dlip/harite-v3/freecad/caps-stickstem09.step

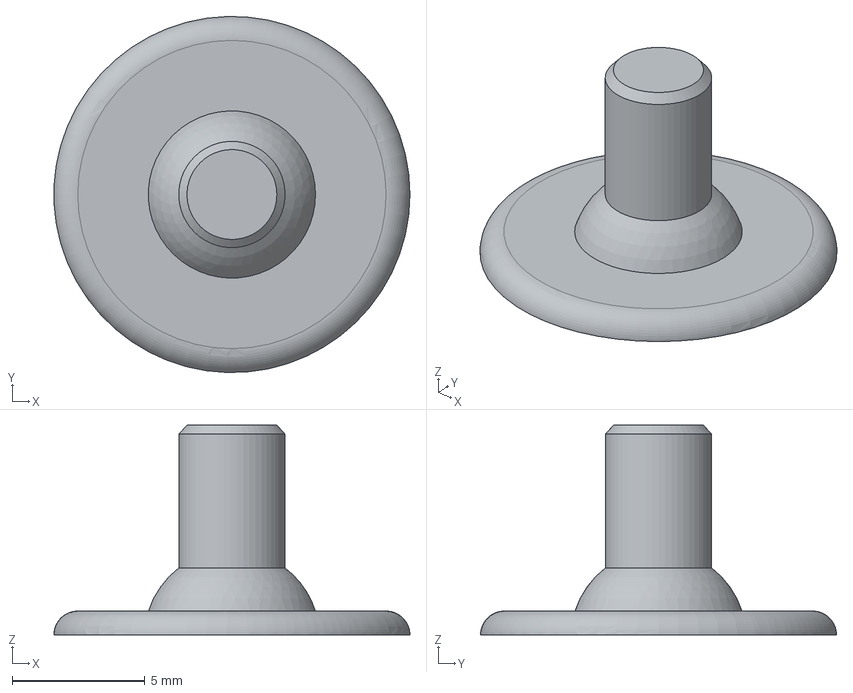
[picture p17: CAD file, 2025-07-30]
freecad/caps-stickstem09.step
13.4 x 13.4 x 7.90 mm
