dlip/harite-v3/freecad/caps-stickstem11.step

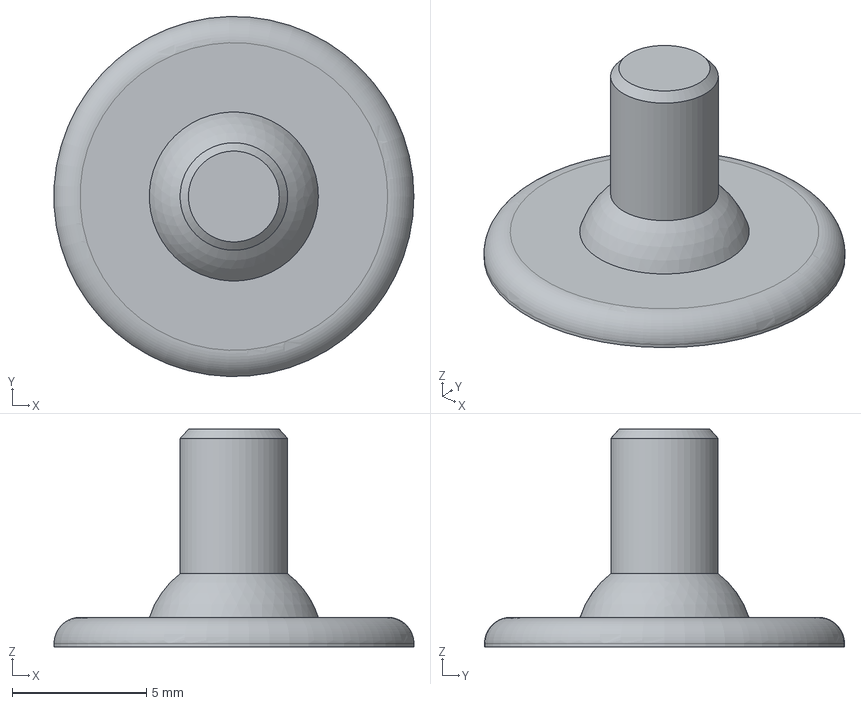
[picture p18: CAD file, 2025-07-30]
freecad/caps-stickstem11.step
13.4 x 13.4 x 8.10 mm
