dlip/harite-v3/freecad/caps-stickstem10.step

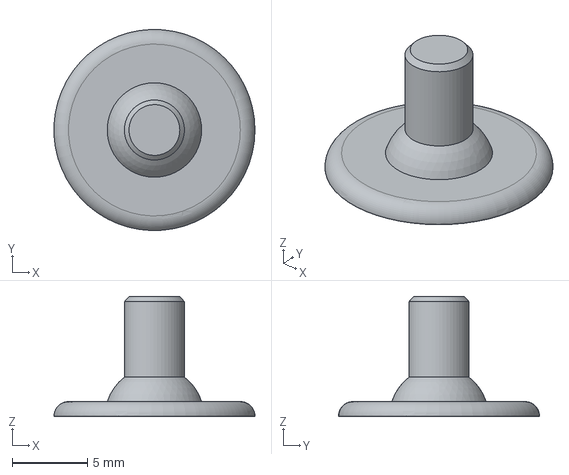
[picture p19: CAD file, 2025-07-30]
freecad/caps-stickstem10.step
13.4 x 13.4 x 8.00 mm
