dlip/harite-v3/freecad/thumb-cluster-casebase-print.step

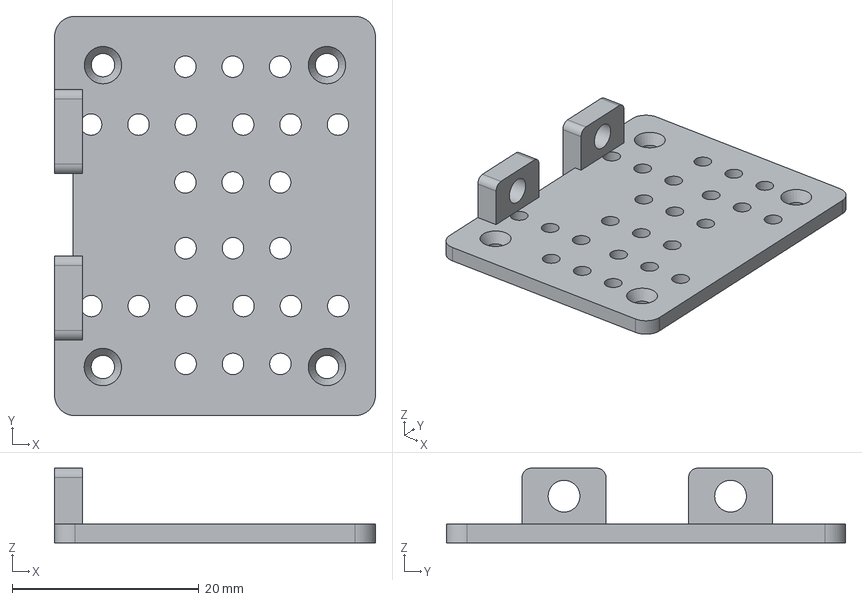
[picture p20: CAD file, 2025-07-30]
freecad/thumb-cluster-casebase-print.step
34.4 x 42.8 x 8.00 mm
