dlip/harite-v3/freecad/thumb-cluster-casetop-stick-print.step

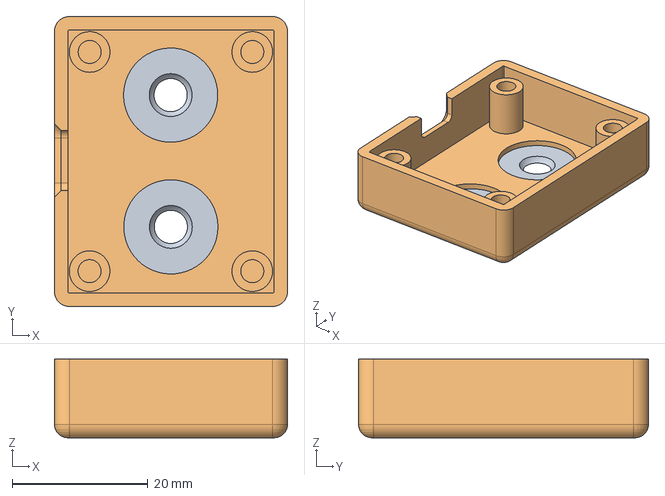
[picture p21: CAD file, 2025-07-30]
freecad/thumb-cluster-casetop-stick-print.step
34.4 x 42.8 x 11.6 mm
stick-recess x 2
top
