dlip/harite-v3/freecad/thumb-cluster.FCStd

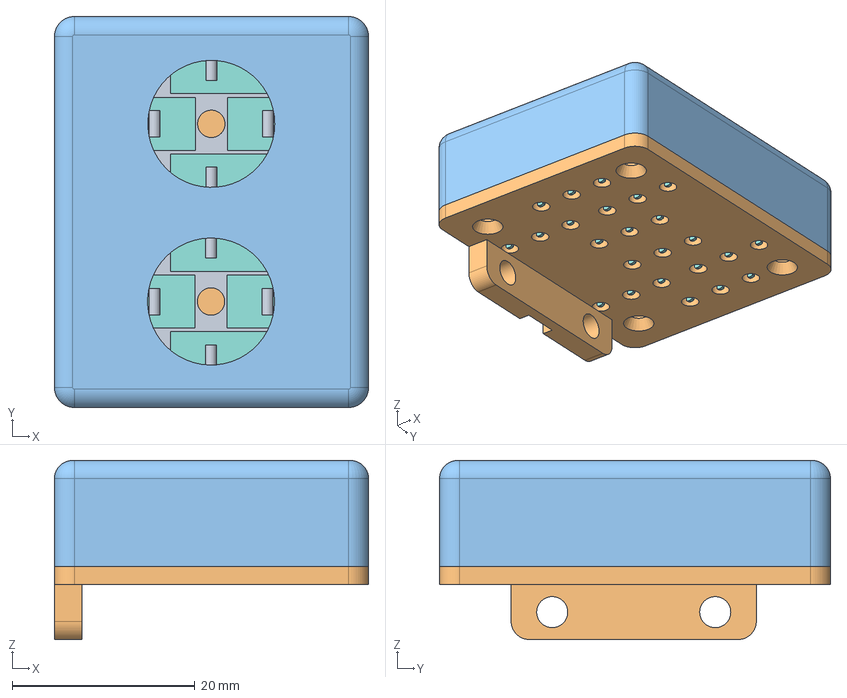
[picture p23: CAD file, 2025-07-30]
freecad/thumb-cluster.FCStd
34.4 x 42.8 x 19.6 mm
Pcb_58ce
D2_SOD-123_L2.8-W1.8-LS3.7-RD-1_65e9c8e63591 x 8
FPC-SMD_P0.50-WS-6P
FPC-SMD_P0.50-WS-6P001
FPC-SMD_P0.50-WS-6P002
FPC-SMD_P0.50-WS-6P003
FPC-SMD_P0.50-WS-6P004
FPC-SMD_P0.50-WS-6P005
FPC-SMD_P0.50-WS-6P006
FPC-SMD_P0.50-WS-6P007
FPC-SMD_P0.50-WS-6P008
FPC-SMD_P0.50-WS-6P009
FPC-SMD_P0.50-WS-6P010
FPC-SMD_P0.50-WS-6P011
FPC-SMD_P0.50-WS-6P012
FPC-SMD_P0.50-WS-6P013
FPC-SMD_P0.50-WS-6P014
FPC-SMD_P0.50-WS-6P015
FPC-SMD_P0.50-WS-6P016
FPC-SMD_P0.50-WS-6P017
FPC-SMD_P0.50-WS-6P018
FPC-SMD_P0.50-WS-6P019
FPC-SMD_P0.50-WS-6P020
D2FC_F_7N_60M_BASE x 8
D2FC_F_7N_60M_BUTTON x 8
base
top
