dlip/harite-v3/freecad/thumb-cluster-casetop-stick.stl

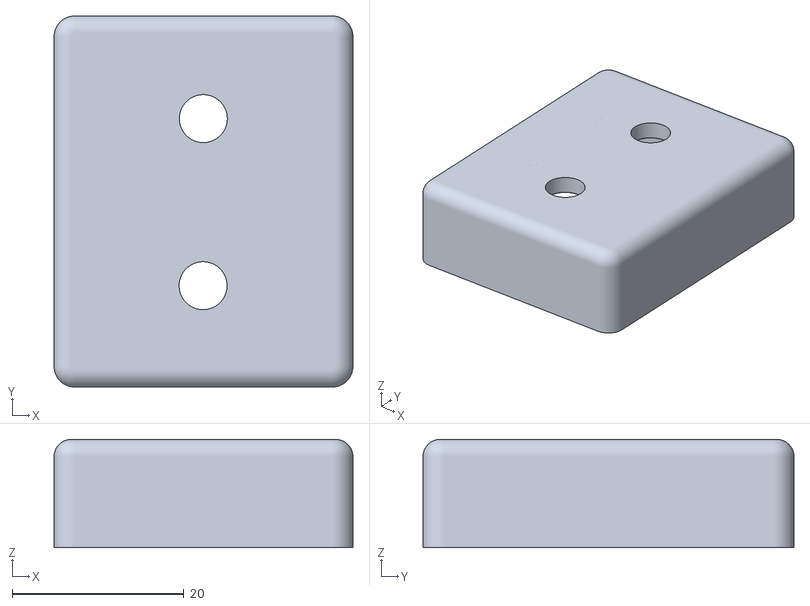
[picture p24: CAD file, 2025-07-23]
freecad/thumb-cluster-casetop-stick.stl
34.8 x 43.2 x 12.6
