dlip/harite-v3/freecad/caps-pivot-bearing.step

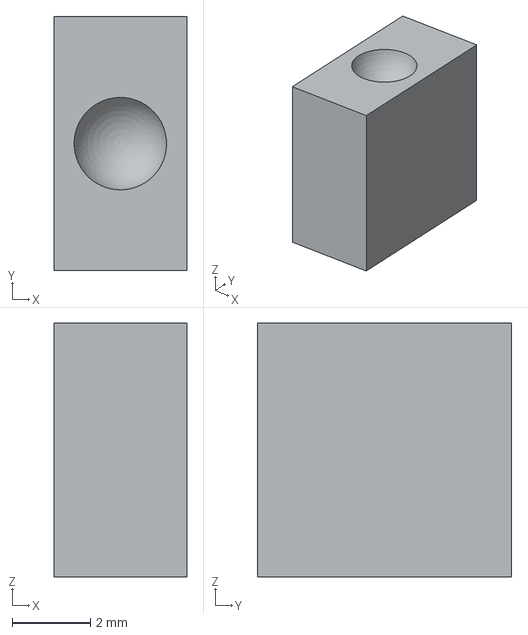
[picture p25: CAD file, 2025-07-23]
freecad/caps-pivot-bearing.step
3.40 x 6.50 x 6.50 mm
