dlip/harite-v3/freecad/caps-stickcap.step

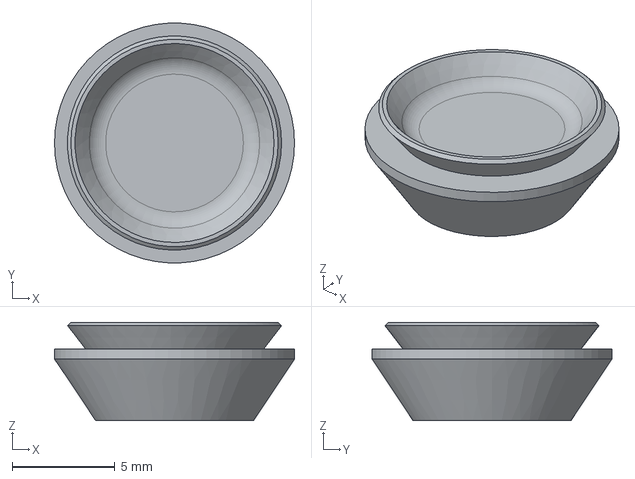
[picture p26: CAD file, 2025-07-23]
freecad/caps-stickcap.step
11.7 x 11.7 x 4.80 mm
