dlip/harite-v3/freecad/caps-stickstick-recess.step

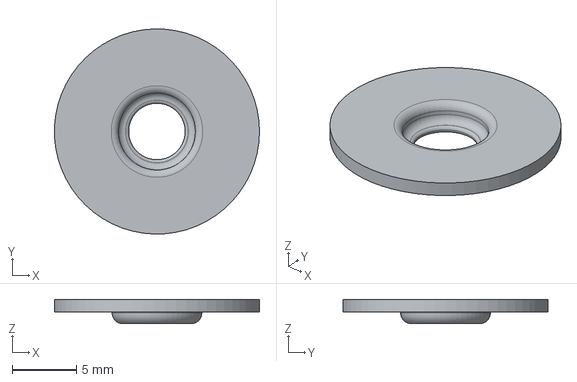
[picture p27: CAD file, 2025-07-23]
freecad/caps-stickstick-recess.step
16.0 x 16.0 x 1.91 mm
