dlip/harite-v3/freecad/thumb-cluster-switch-aligner-print.step

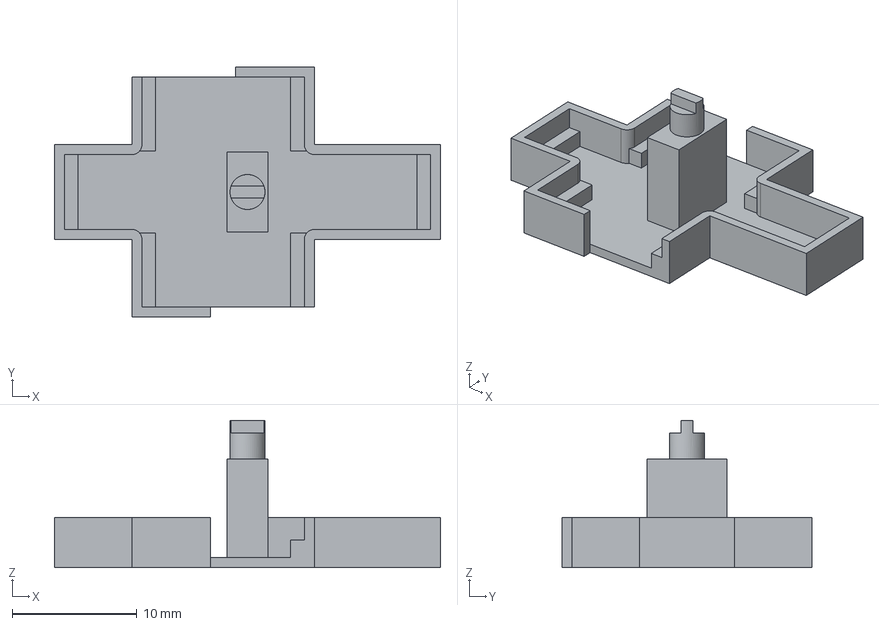
[picture p28: CAD file, 2025-07-23]
freecad/thumb-cluster-switch-aligner-print.step
30.9 x 20.0 x 11.8 mm
