dlip/harite-v3/freecad/thumb-cluster-test-base.step

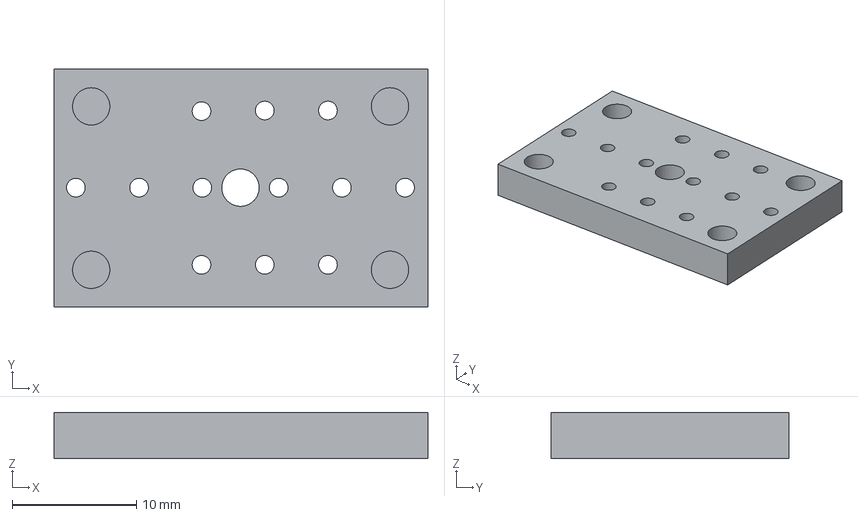
[picture p29: CAD file, 2025-07-23]
freecad/thumb-cluster-test-base.step
30.1 x 19.1 x 3.70 mm
